0ddjob/Nafanya/Images/Nafanya_Keyboard_3.jpeg

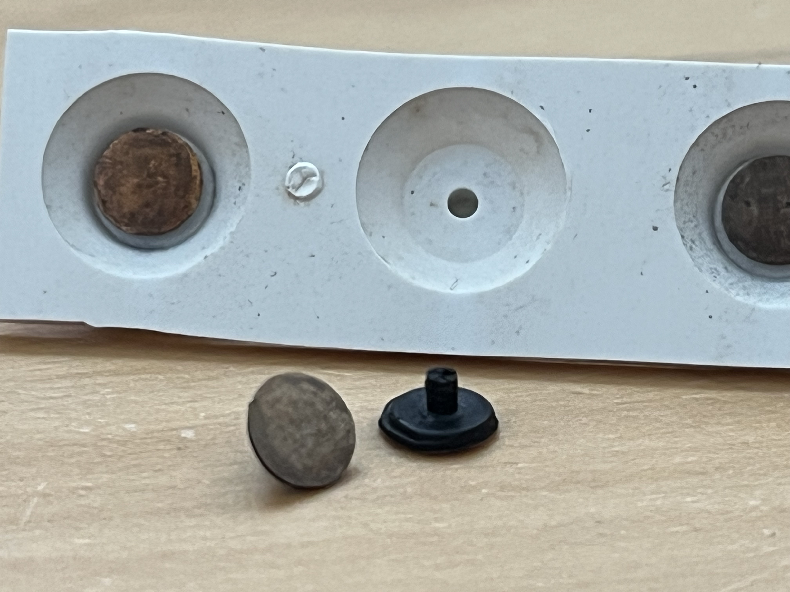
Images/Nafanya_Keyboard_3.jpeg
