0ddjob/Nafanya/Images/Nafanya_Keyboard_5.jpeg

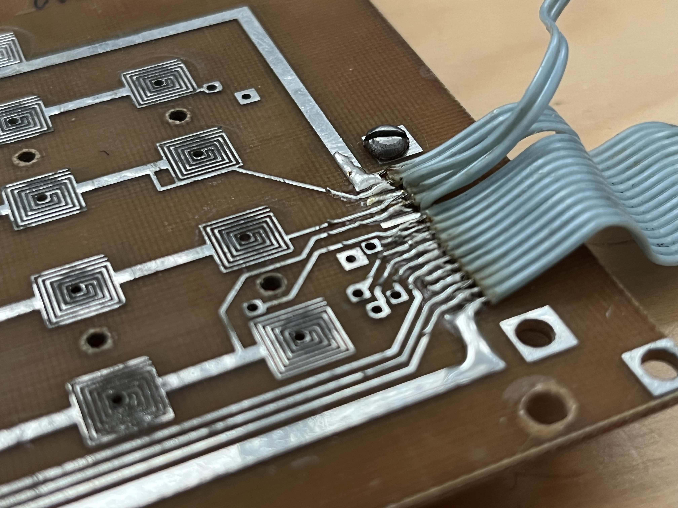
Images/Nafanya_Keyboard_5.jpeg
