0ddjob/Nafanya/Images/Nafanya_Keyboard_6.jpeg

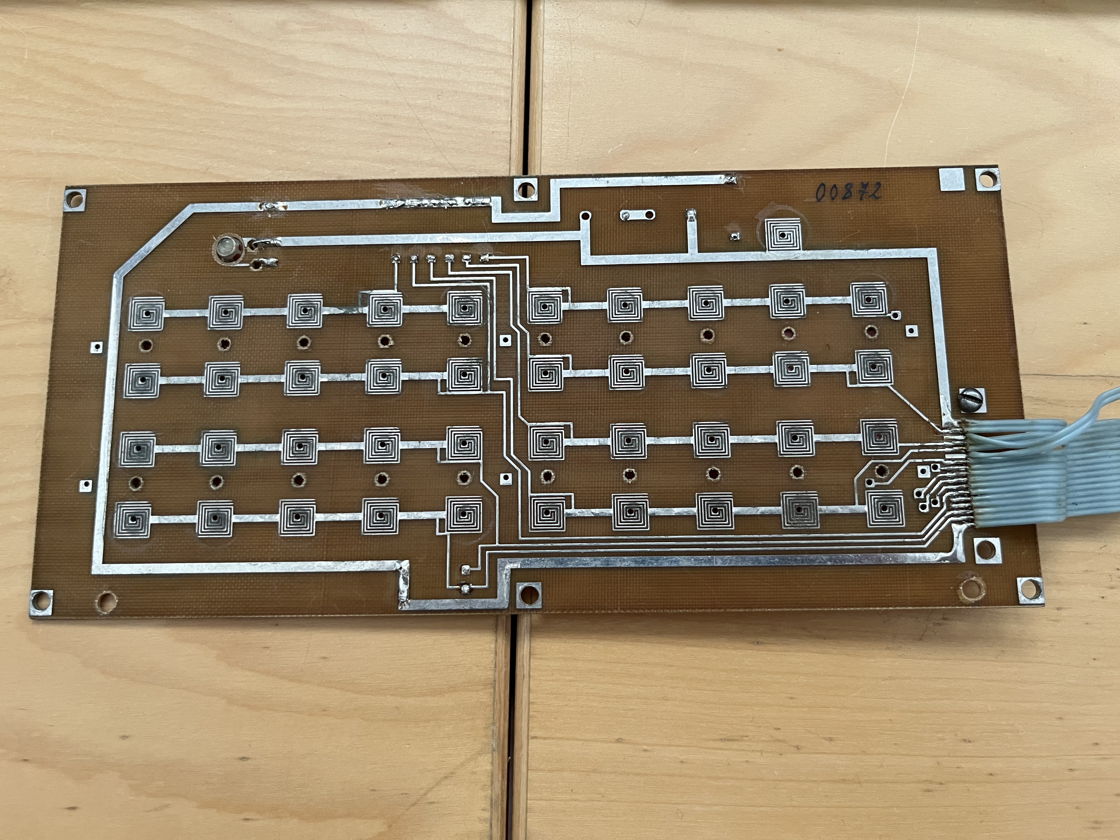
Images/Nafanya_Keyboard_6.jpeg
