0ddjob/Nafanya/Images/Nafanya_Keyboard_7.jpeg

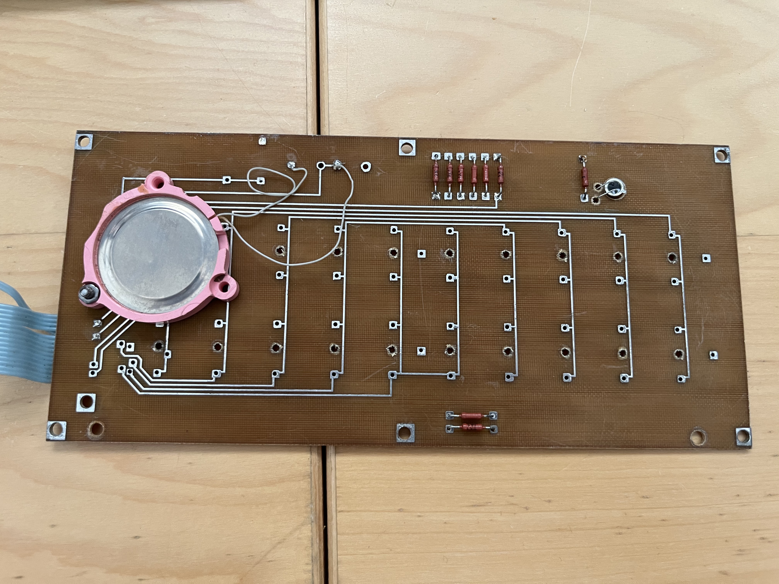
Images/Nafanya_Keyboard_7.jpeg
