0ddjob/Nafanya/Images/Nafanya_Keyboard_8.jpeg

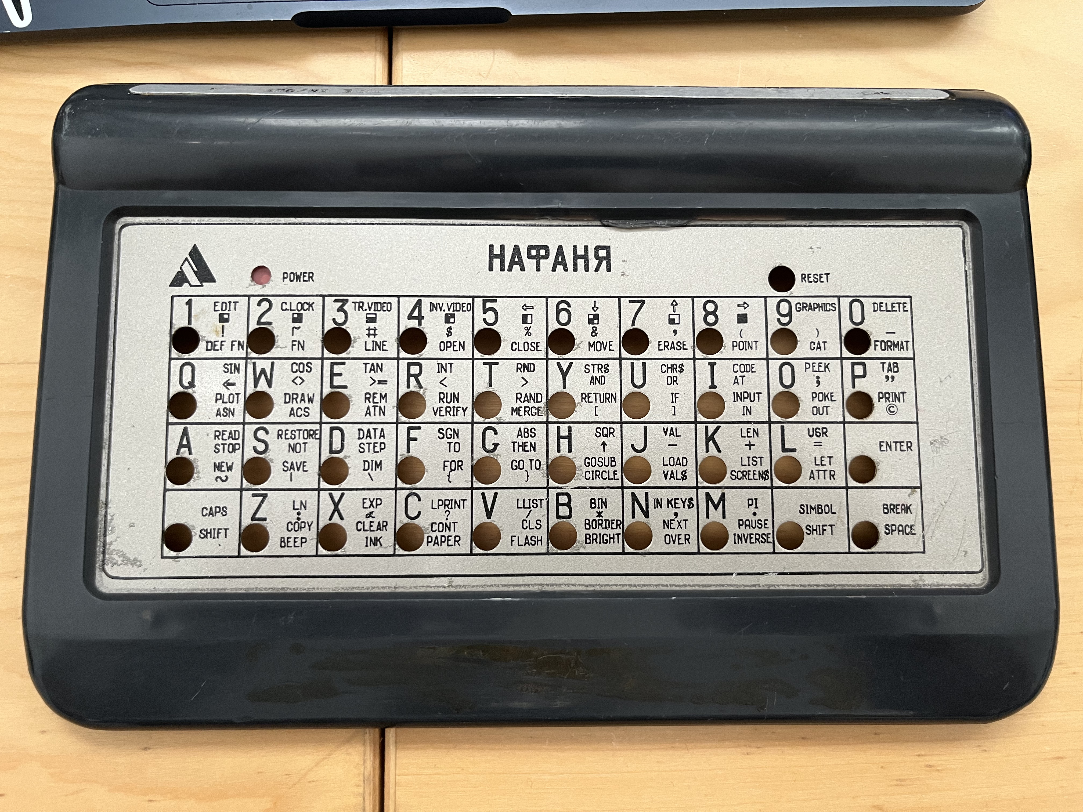
Images/Nafanya_Keyboard_8.jpeg
