0ddjob/Nafanya/Images/Nafanya_keyboard_connectors_cleaned.jpeg

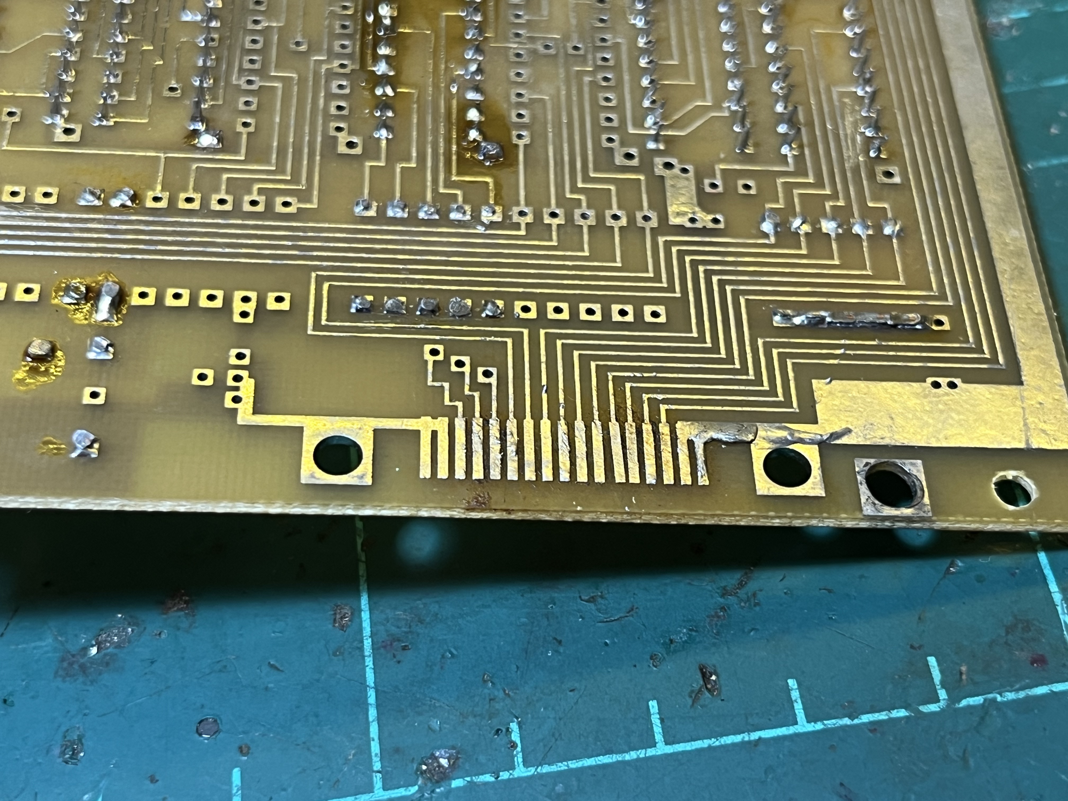
Images/Nafanya_keyboard_connectors_cleaned.jpeg
