0ddjob/Nafanya/Images/Nafanya_Video_circuit_1.jpeg

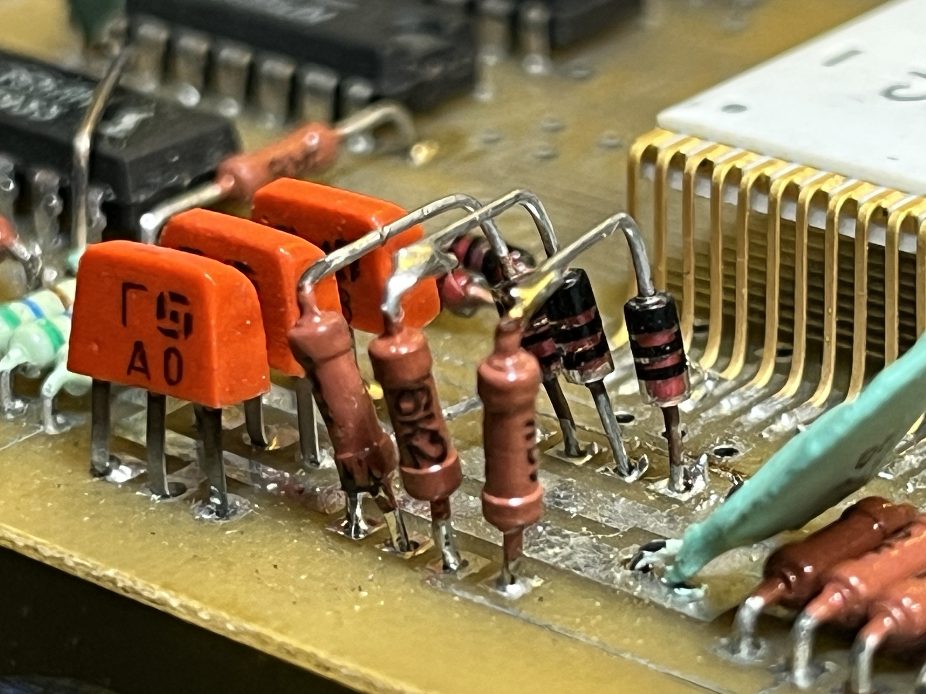
Images/Nafanya_Video_circuit_1.jpeg
