0ddjob/Nafanya/Images/Nafanya_Video_circuit_2.jpeg

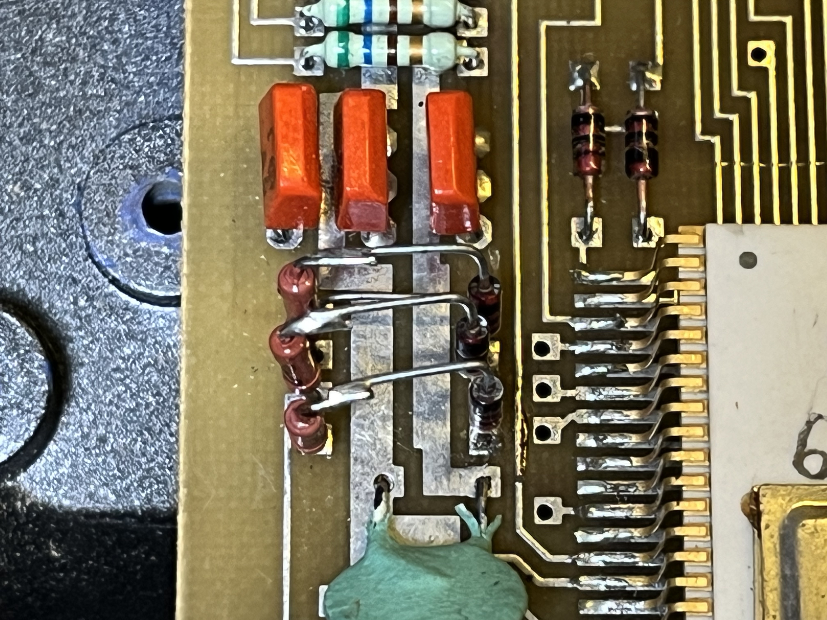
Images/Nafanya_Video_circuit_2.jpeg
