0ddjob/Nafanya/Images/Nafanya_Video_circuit_3.jpeg

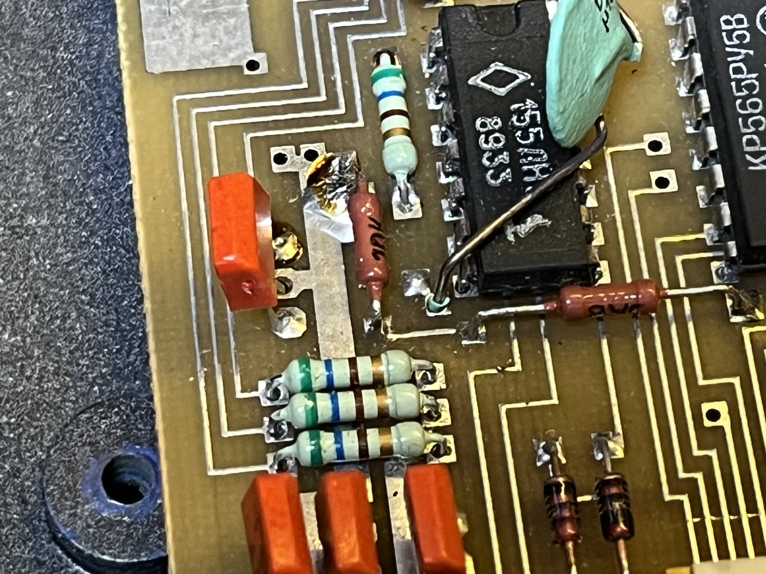
Images/Nafanya_Video_circuit_3.jpeg
