0ddjob/Nafanya/Images/Nafanya_keyboard_wiring_motherboard.jpeg

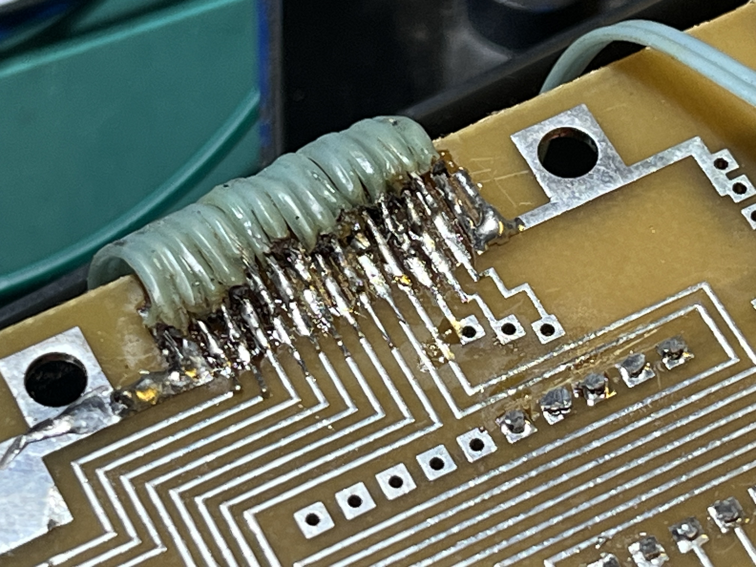
Images/Nafanya_keyboard_wiring_motherboard.jpeg
