0ddjob/Nafanya/Images/Nafanya_Speaker_wiring_motherboard.jpeg

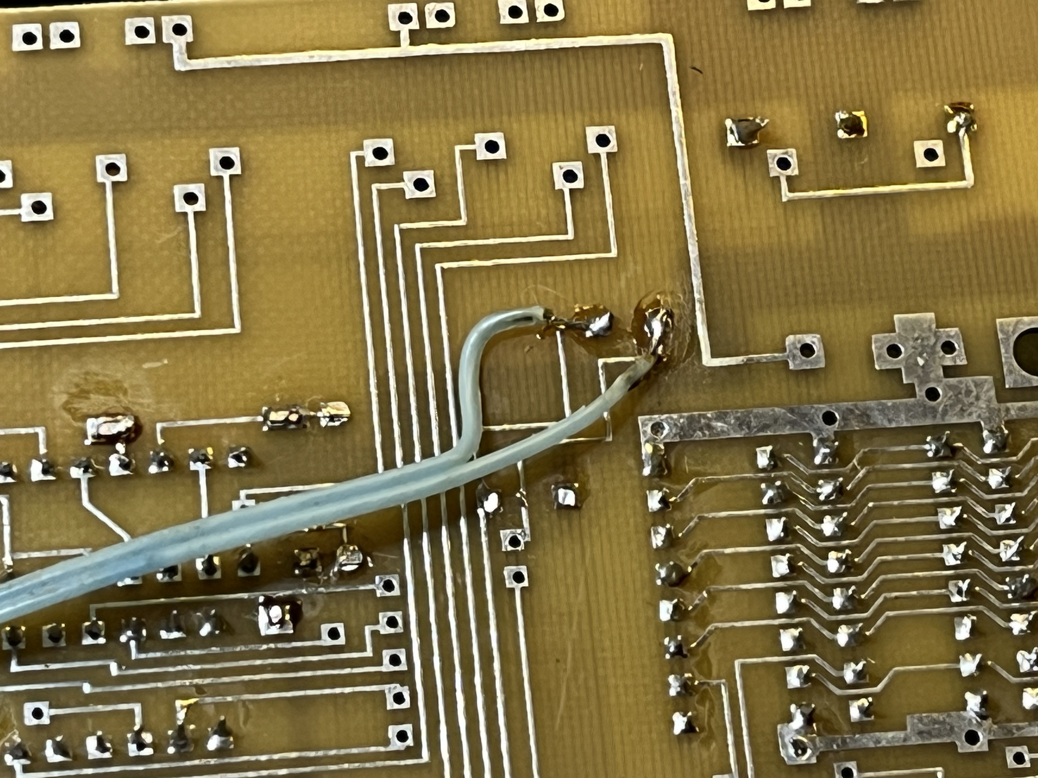
Images/Nafanya_Speaker_wiring_motherboard.jpeg
